mlab-modules/ADSBAFE01/doc/gen/dxf/ADSBAFE01-F_Cu.dxf

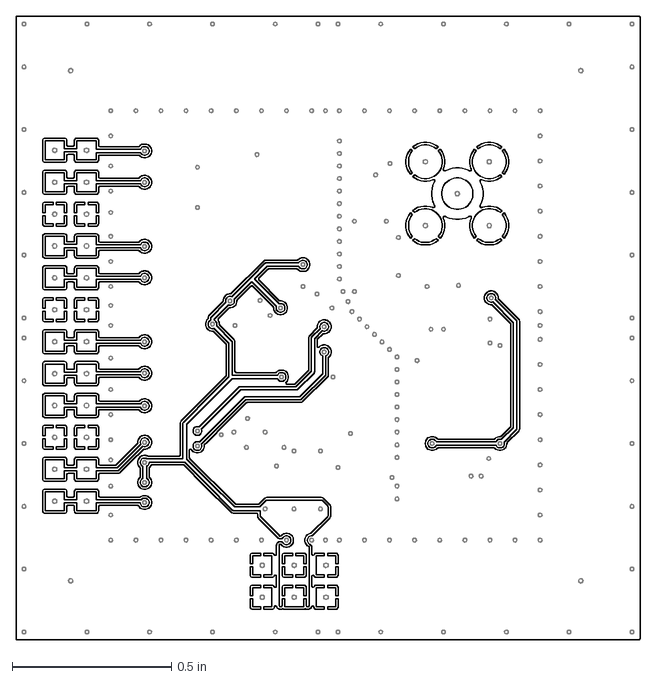
[picture p9: CAD file, 2026-05-16]
doc/gen/dxf/ADSBAFE01-F_Cu.dxf
1.96 x 1.96 in
