mlab-modules/ADSBAFE01/doc/gen/dxf/ADSBAFE01-Edge_Cuts.dxf

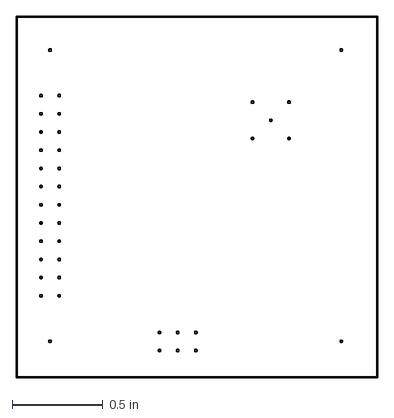
[picture p10: CAD file, 2026-05-16]
doc/gen/dxf/ADSBAFE01-Edge_Cuts.dxf
1.99 x 1.99 in
