mlab-modules/ADSBAFE01/doc/gen/dxf/ADSBAFE01-B_Courtyard.dxf

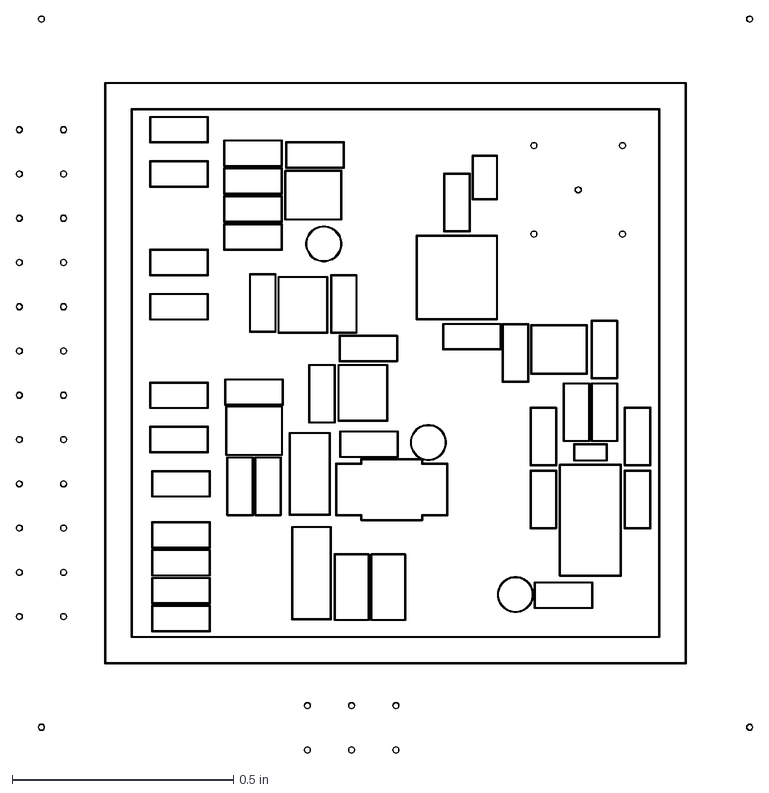
[picture p11: CAD file, 2026-05-16]
doc/gen/dxf/ADSBAFE01-B_Courtyard.dxf
1.66 x 1.66 in
